mistic100/HyperCube/SolidWorks/HyperCubeAndCase.SLDASM

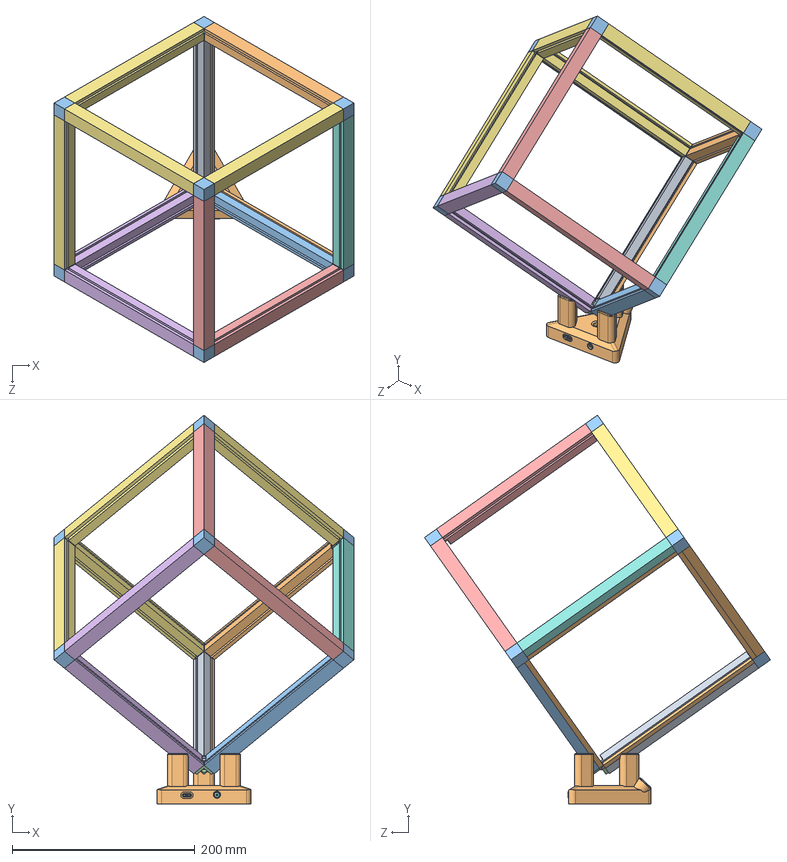
[picture p7: CAD file, 2025-02-01]
SolidWorks/HyperCubeAndCase.SLDASM
328.1 x 425.5 x 378.9 mm
electronics-case-support
WEMOS-D1-mini_detailed
main_body
jack_outer_metal
jack_inner_rod
wireholder x 2
corner-bottom x 4
beam-bottom
beam-bottom-w-hole
beam-bottom-w-hole_symetry
beam-bottom_symetry
beam-base x 4
beam-w-hole x 2
beam x 2
corner x 4
corner-cache x 7
panel-holder x 4
button
