mistic100/HyperCube/SolidWorks/HyperCube.SLDASM

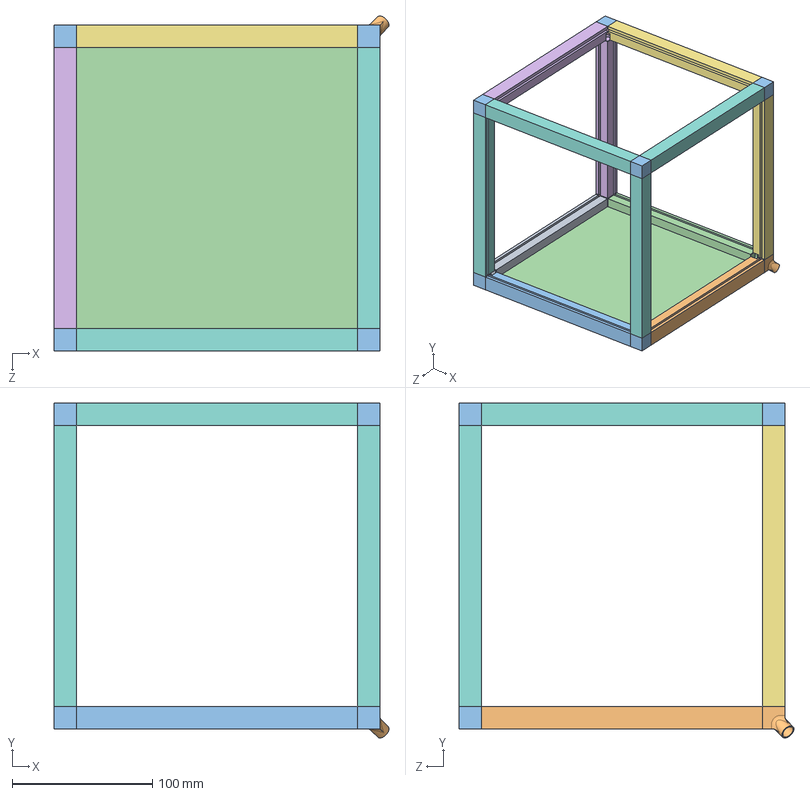
[picture p9: CAD file, 2025-02-01]
SolidWorks/HyperCube.SLDASM
238.6 x 238.6 x 238.6 mm
corner-bottom x 4
beam-bottom
beam-bottom-w-hole
beam-bottom-w-hole_symetry
beam-bottom_symetry
beam-base x 4
beam-w-hole x 2
beam x 2
corner x 4
glass
corner-cache x 7
corner-cache-w-hole
panel-holder x 4
