mistic100/HyperCube/SolidWorks/5-5-x-2-1mm-dc-power-female-jack-connector-plug-1.snapshot.2/jack_inner_rod.SLDPRT

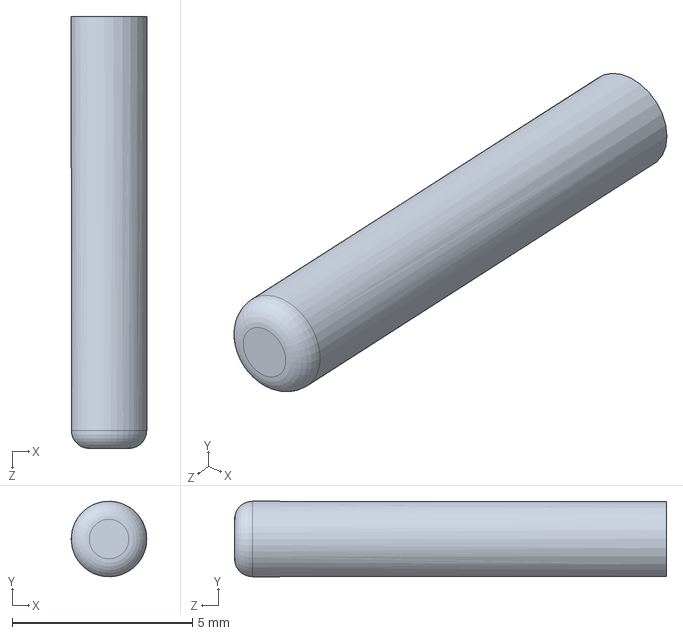
[picture p22: CAD file, 2020-08-25]
SolidWorks/5-5-x-2-1mm-dc-power-female-jack-connector-plug-1.snapshot.2/jack_inner_rod.SLDPRT
2.10 x 2.10 x 12.0 mm
