mistic100/HyperCube/SolidWorks/beam-bottom.SLDPRT

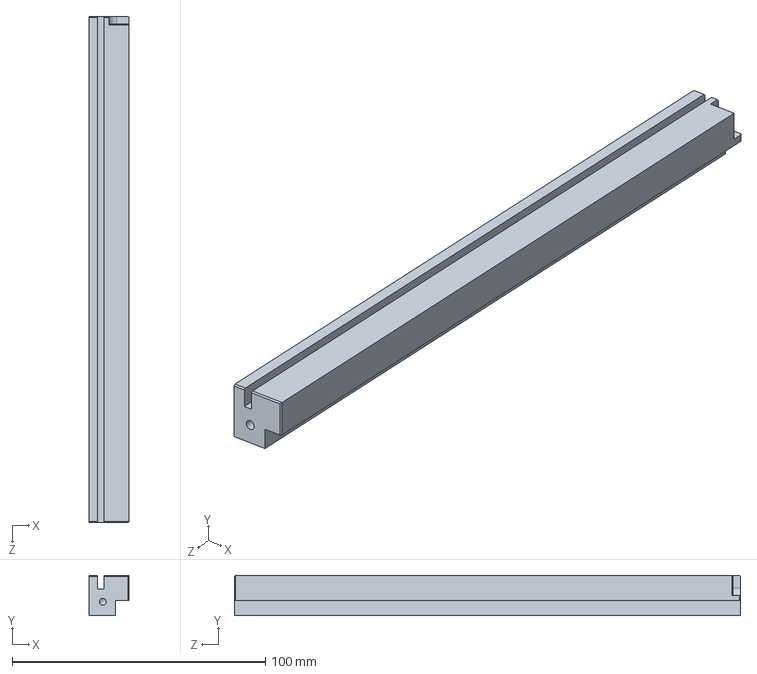
[picture p23: CAD file, 2025-02-01]
SolidWorks/beam-bottom.SLDPRT
16.0 x 16.0 x 200.0 mm
