mistic100/HyperCube/STL/corner-cache (x5).STL

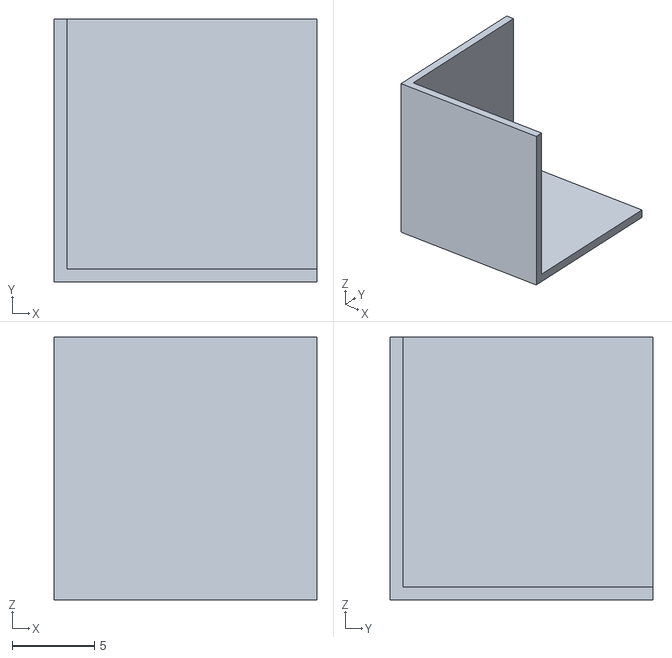
[picture p24: CAD file, 2020-08-25]
STL/corner-cache (x5).STL
16.0 x 16.0 x 16.0
