mistic100/HyperCube/STL/beam-bottom-w-hole (x1 + 1 symmetry).STL

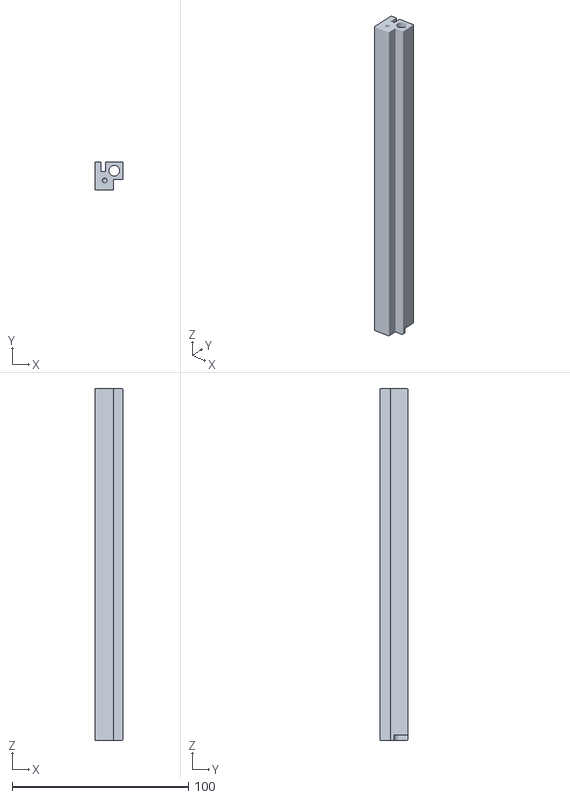
[picture p25: CAD file, 2020-08-09]
STL/beam-bottom-w-hole (x1 + 1 symmetry).STL
16.0 x 16.0 x 200.0
