mistic100/HyperCube/STL/beam-w-hole (x2).STL

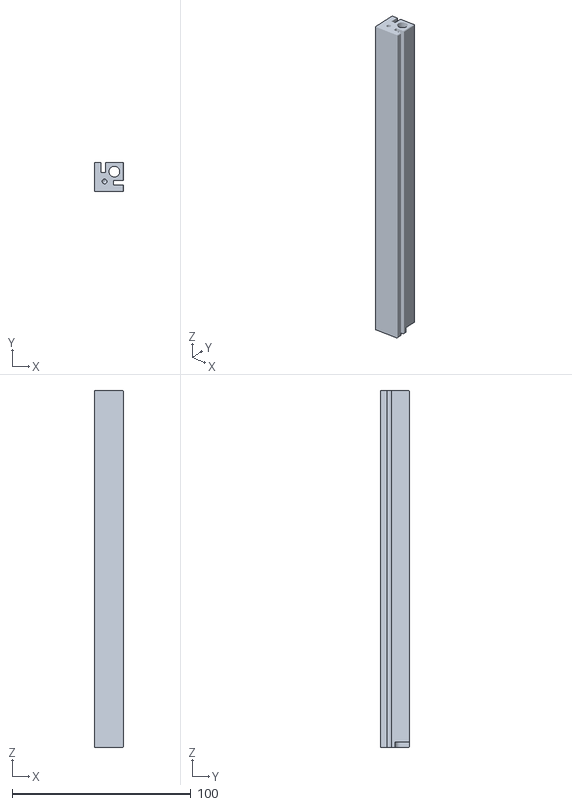
[picture p26: CAD file, 2020-08-09]
STL/beam-w-hole (x2).STL
16.0 x 16.0 x 200.0
